SukkoPera/WheelOfJoy/img/4.png

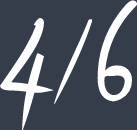
img/4.png
