SukkoPera/WheelOfJoy/img/6.png

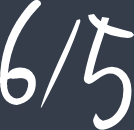
img/6.png
