SukkoPera/WheelOfJoy/img/7.png

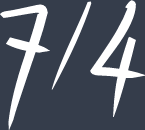
img/7.png
